katielukow/MBPF/CAD/Fastener CAD/90690A047_BRASS HEX NUT.SLDPRT

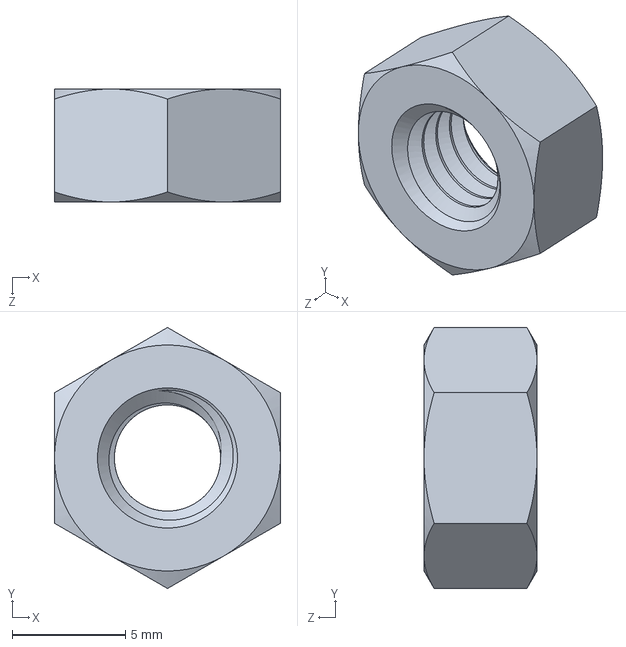
[picture p18: CAD file, 2021-06-02]
CAD/Fastener CAD/90690A047_BRASS HEX NUT.SLDPRT
10.0 x 11.5 x 5.00 mm
